Chris-Johnston/BinaryKeyboard/Eagle/BinaryKeyboard.sch

## EAGLE design Eagle/BinaryKeyboard.sch (2017-04-14)

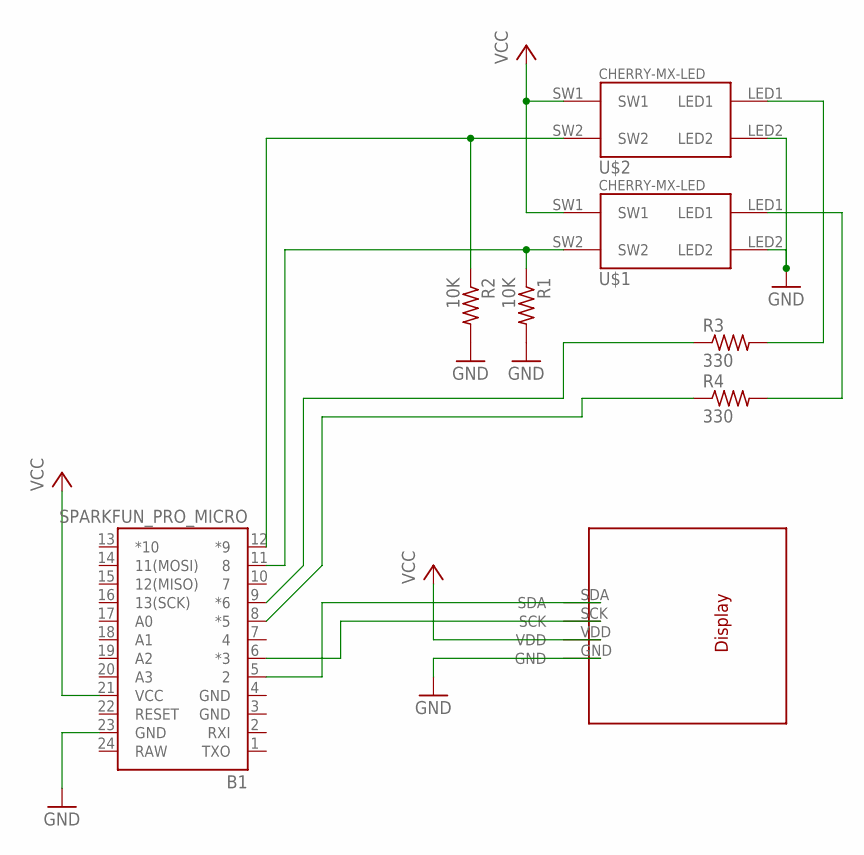
[picture p6: schematic BinaryKeyboard.sch]

Parts:
B1: SPARKFUN_PRO_MICRO
DISPLAY1: GM009605
R1, R2: 10K; 0204/7
R3, R4: 330; 0204/7
U$1, U$2: CHERRY-MX-LED

Connections:
GND: B1.23 (GND), DISPLAY1.GND, R1.2, R2.2, U$1.LED2, U$2.LED2
unnamed: B1.11 (8), R1.1, U$1.SW2
unnamed: B1.12 (*9), R2.1, U$2.SW2
unnamed: B1.5 (2), DISPLAY1.SDA
unnamed: B1.6 (*3), DISPLAY1.SCK
unnamed: R3.2, U$2.LED1
unnamed: R4.2, U$1.LED1
unnamed: B1.9 (*6), R3.1
unnamed: B1.8 (*5), R4.1
VCC: B1.21 (VCC), DISPLAY1.VDD, U$1.SW1, U$2.SW1
